fgcoca/Basic-Input-Output-Shield-Arduino-UNO/images/20191013_120853.jpg

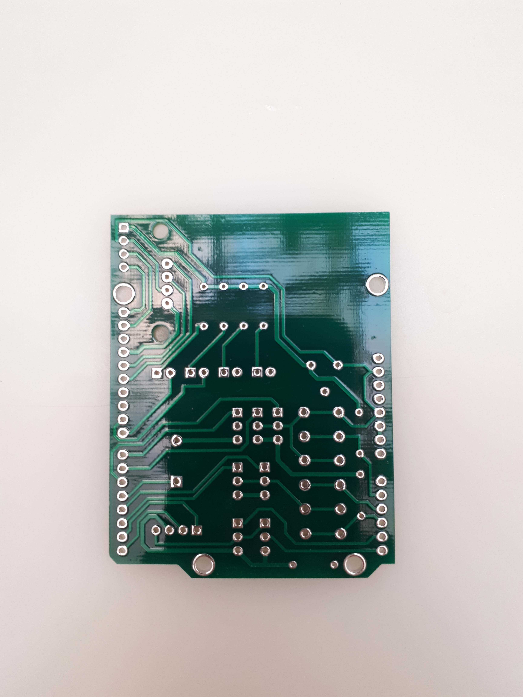
images/20191013_120853.jpg
