fgcoca/Basic-Input-Output-Shield-Arduino-UNO/images/20191013_120941.jpg

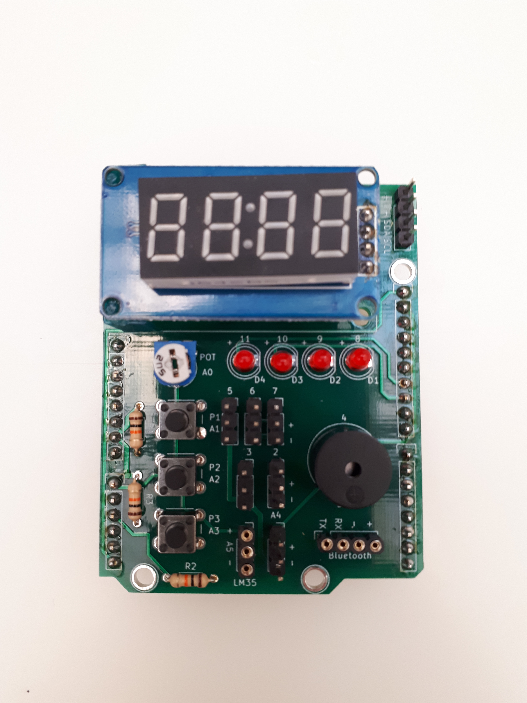
images/20191013_120941.jpg
