fgcoca/Basic-Input-Output-Shield-Arduino-UNO/images/20191013_121113.jpg

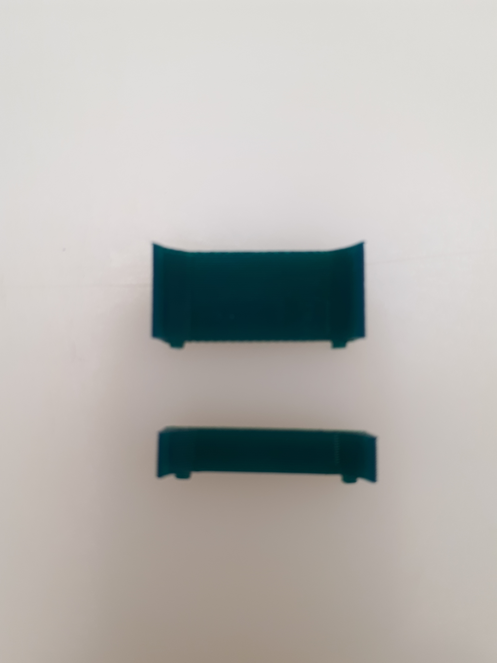
images/20191013_121113.jpg
